gugray/Shizhong/code/src/events.h

#ifndef EVENTS_H
#define EVENTS_H

#define EVT_ENTER_FACE 0x0001
#define EVT_SECOND_TICK 0x0002
#define EVT_QUICK_TICK 0x0004

#define EVT_BTN_MODE_DOWN 0x0008
#define EVT_BTN_MODE_REPEAT 0x0010
#define EVT_BTN_MODE_SHORT 0x0020
#define EVT_BTN_MODE_LONG 0x0040

#define EVT_BTN_PLUS_DOWN 0x0080
#define EVT_BTN_PLUS_REPEAT 0x0100
#define EVT_BTN_PLUS_SHORT 0x0200
#define EVT_BTN_PLUS_LONG 0x0400

#define EVT_BTN_MINUS_DOWN 0x0800
#define EVT_BTN_MINUS_REPEAT 0x1000
#define EVT_BTN_MINUS_SHORT 0x2000
#define EVT_BTN_MINUS_LONG 0x4000

#define ISEVENT(EVT) (event & EVT) != 0

#define RET_STAY 1
#define RET_NEXT 2
#define RET_HOME 3

#endif
